Victor-BENOIT/Mission-Unsleepable/Final Version (French)/Code/Actionneur/Buttons/buttons.h

/*
 * buttons.h
 * Purpose : Gérer la pression des boutons poussoirs
 *
 *  Created on: 17/11/2022
 *  Author: Bigot
 */


#ifndef BUTTONS_H_
#define BUTTONS_H_

#include "macro_types.h"


bool_e button_left_press_event(void);
bool_e button_center_press_event(void);
bool_e button_right_press_event(void);

#endif
