Victor-BENOIT/Mission-Unsleepable/Final Version (French)/Code/Actionneur/HCSR04/hcsr04.h

/*
 * hcsr04.h
 * Purpose : Gerer le module HCSR04
 *
 *  Created on: 17/11/2022
 *  Author: Bigot
 */

#ifndef HCSR04_H_
#define HCSR04_H_

#include "HC-SR04/HCSR04.h"

void hcsr04_state_machine(void);

#endif
